pingyi/ZSWatch-HW/production/watch-dk-CHECKED/HTML/images/cat_pdf_drill_map_ZSWatch-Watch-DevKit-PTH_drill_map.png

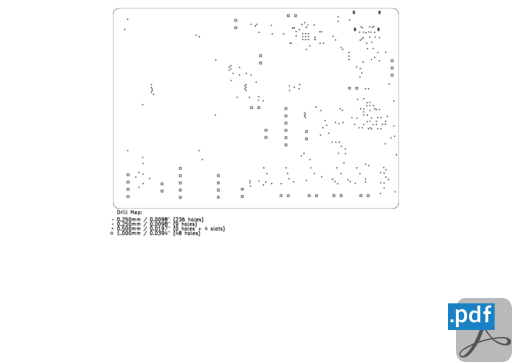
production/watch-dk-CHECKED/HTML/images/cat_pdf_drill_map_ZSWatch-Watch-DevKit-PTH_drill_map.png
