pingyi/ZSWatch-HW/production/watch-dk-CHECKED/HTML/images/cat_png_3d_viewer_top_ZSWatch-Watch-DevKit-top.png

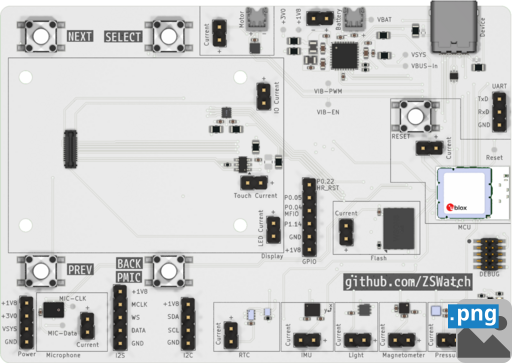
production/watch-dk-CHECKED/HTML/images/cat_png_3d_viewer_top_ZSWatch-Watch-DevKit-top.png
